scarytom/train-control/ref/RBT DIN Socket Wiring.png

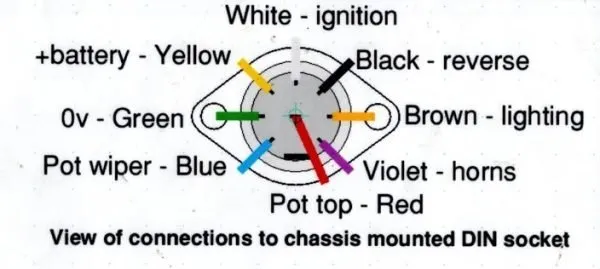
ref/RBT DIN Socket Wiring.png
